alentar/mediot-hardware/PCB/board2.sch

## EAGLE design PCB/board2.sch (2018-06-13)

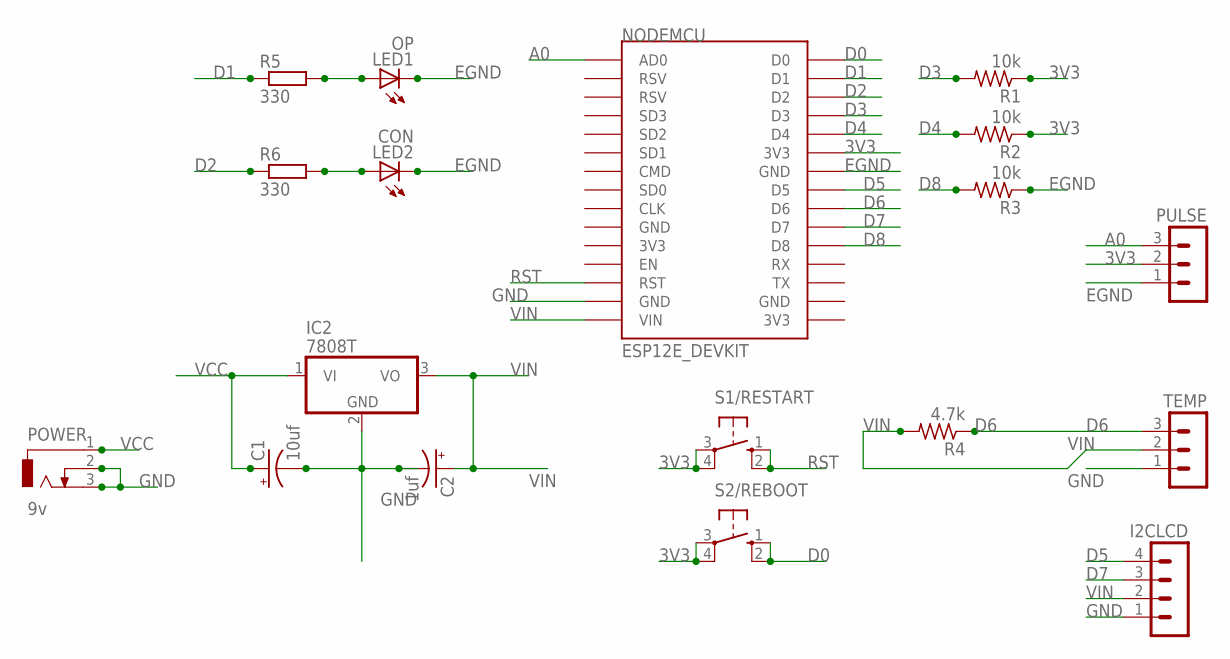
[picture p3: schematic board2.sch]

Parts:
C1: 10uf; E2,5-5
C2: 1uf; E2,5-5
I2CLCD: MA04-1
IC2: 7808T; TO220H
LED1: OP; LED3MM
LED2: CON; LED3MM
NODEMCU: ESP12E_DEVKIT
POWER: 9v; DCJ0303
PULSE: MA03-1
R1, R2, R3: 10k; 0207/7
R4: 4.7k; 0207/7
R5, R6: 330; 0204/5
S1/RESTART, S2/REBOOT: 10-XX; B3F-10XX
TEMP: MA03-1

Connections:
3V3: NODEMCU.3V3@1 (3V3), PULSE.2, R1.1, R2.1, S1/RESTART.3, S1/RESTART.4 (P1), S2/REBOOT.3, S2/REBOOT.4 (P1)
A0: NODEMCU.AD0, PULSE.3
D0: NODEMCU.D0, S2/REBOOT.1 (S), S2/REBOOT.2 (S1)
D1: NODEMCU.D1, R5.1
D2: NODEMCU.D2, R6.1
D3: NODEMCU.D3, R1.2
D4: NODEMCU.D4, R2.2
D5: I2CLCD.4, NODEMCU.D5
D6: NODEMCU.D6, R4.1, TEMP.3
D7: I2CLCD.3, NODEMCU.D7
D8: NODEMCU.D8, R3.2
EGND: LED1.K (C), LED2.K (C), NODEMCU.GND@2 (GND), PULSE.1, R3.1
GND: C1.-, C2.-, I2CLCD.1, IC2.2 (GND), NODEMCU.GND@1 (GND), POWER.2, POWER.3, TEMP.1
unnamed: LED1.A, R5.2
unnamed: LED2.A, R6.2
RST: NODEMCU.RST, S1/RESTART.1 (S), S1/RESTART.2 (S1)
VCC: C1.+, IC2.1 (VI), POWER.1
VIN: C2.+, I2CLCD.2, IC2.3 (VO), NODEMCU.VIN, R4.2, TEMP.2
